MildRacc/MildVR/PCB/Imports/SFH_4556/SFH_4556.step

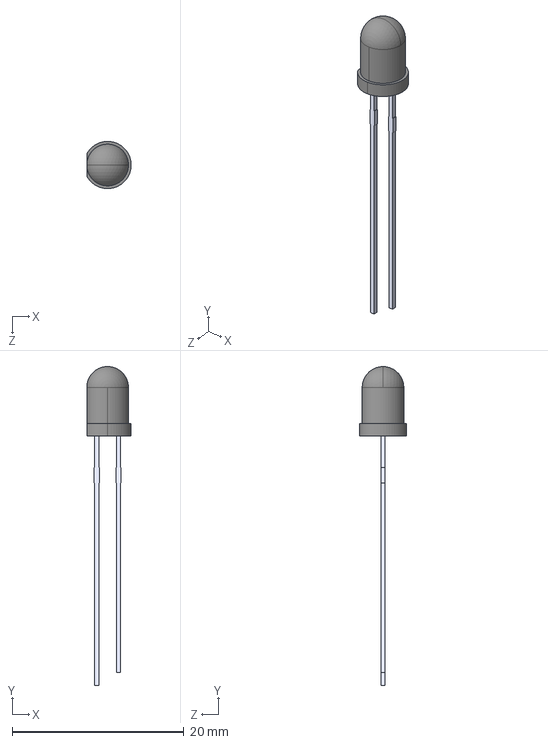
[picture p15: CAD file, 2025-12-30]
PCB/Imports/SFH_4556/SFH_4556.step
5.18 x 37.1 x 5.50 mm
