MildRacc/MildVR/PCB/Imports/(CSI) 20539-050E-01/20539-050E-01.step

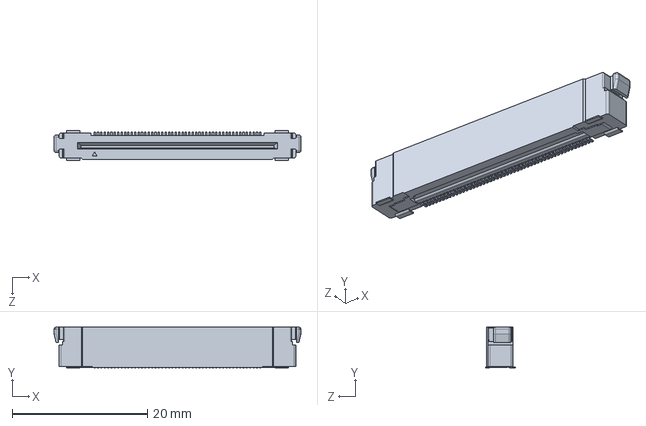
[picture p16: CAD file, 2025-11-03]
PCB/Imports/(CSI) 20539-050E-01/20539-050E-01.step
36.5 x 6.00 x 4.50 mm
