MildRacc/MildVR/PCB/Imports/(Pump)LM27761DSGR/LM27761DSGR.step

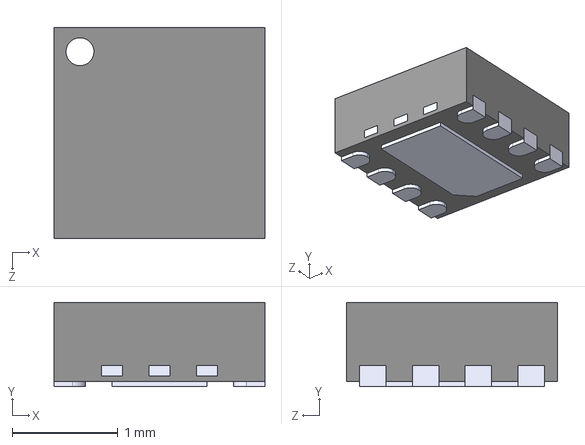
[picture p17: CAD file, 2025-12-31]
PCB/Imports/(Pump)LM27761DSGR/LM27761DSGR.step
2.00 x 0.8 x 2.00 mm
