MildRacc/MildVR/PCB/Imports/CM4IO-KiCAD/CM4_HighSpeed.kicad_sch

## KiCad design PCB/Imports/CM4IO-KiCAD/CM4_HighSpeed.kicad_sch (2025-11-22)

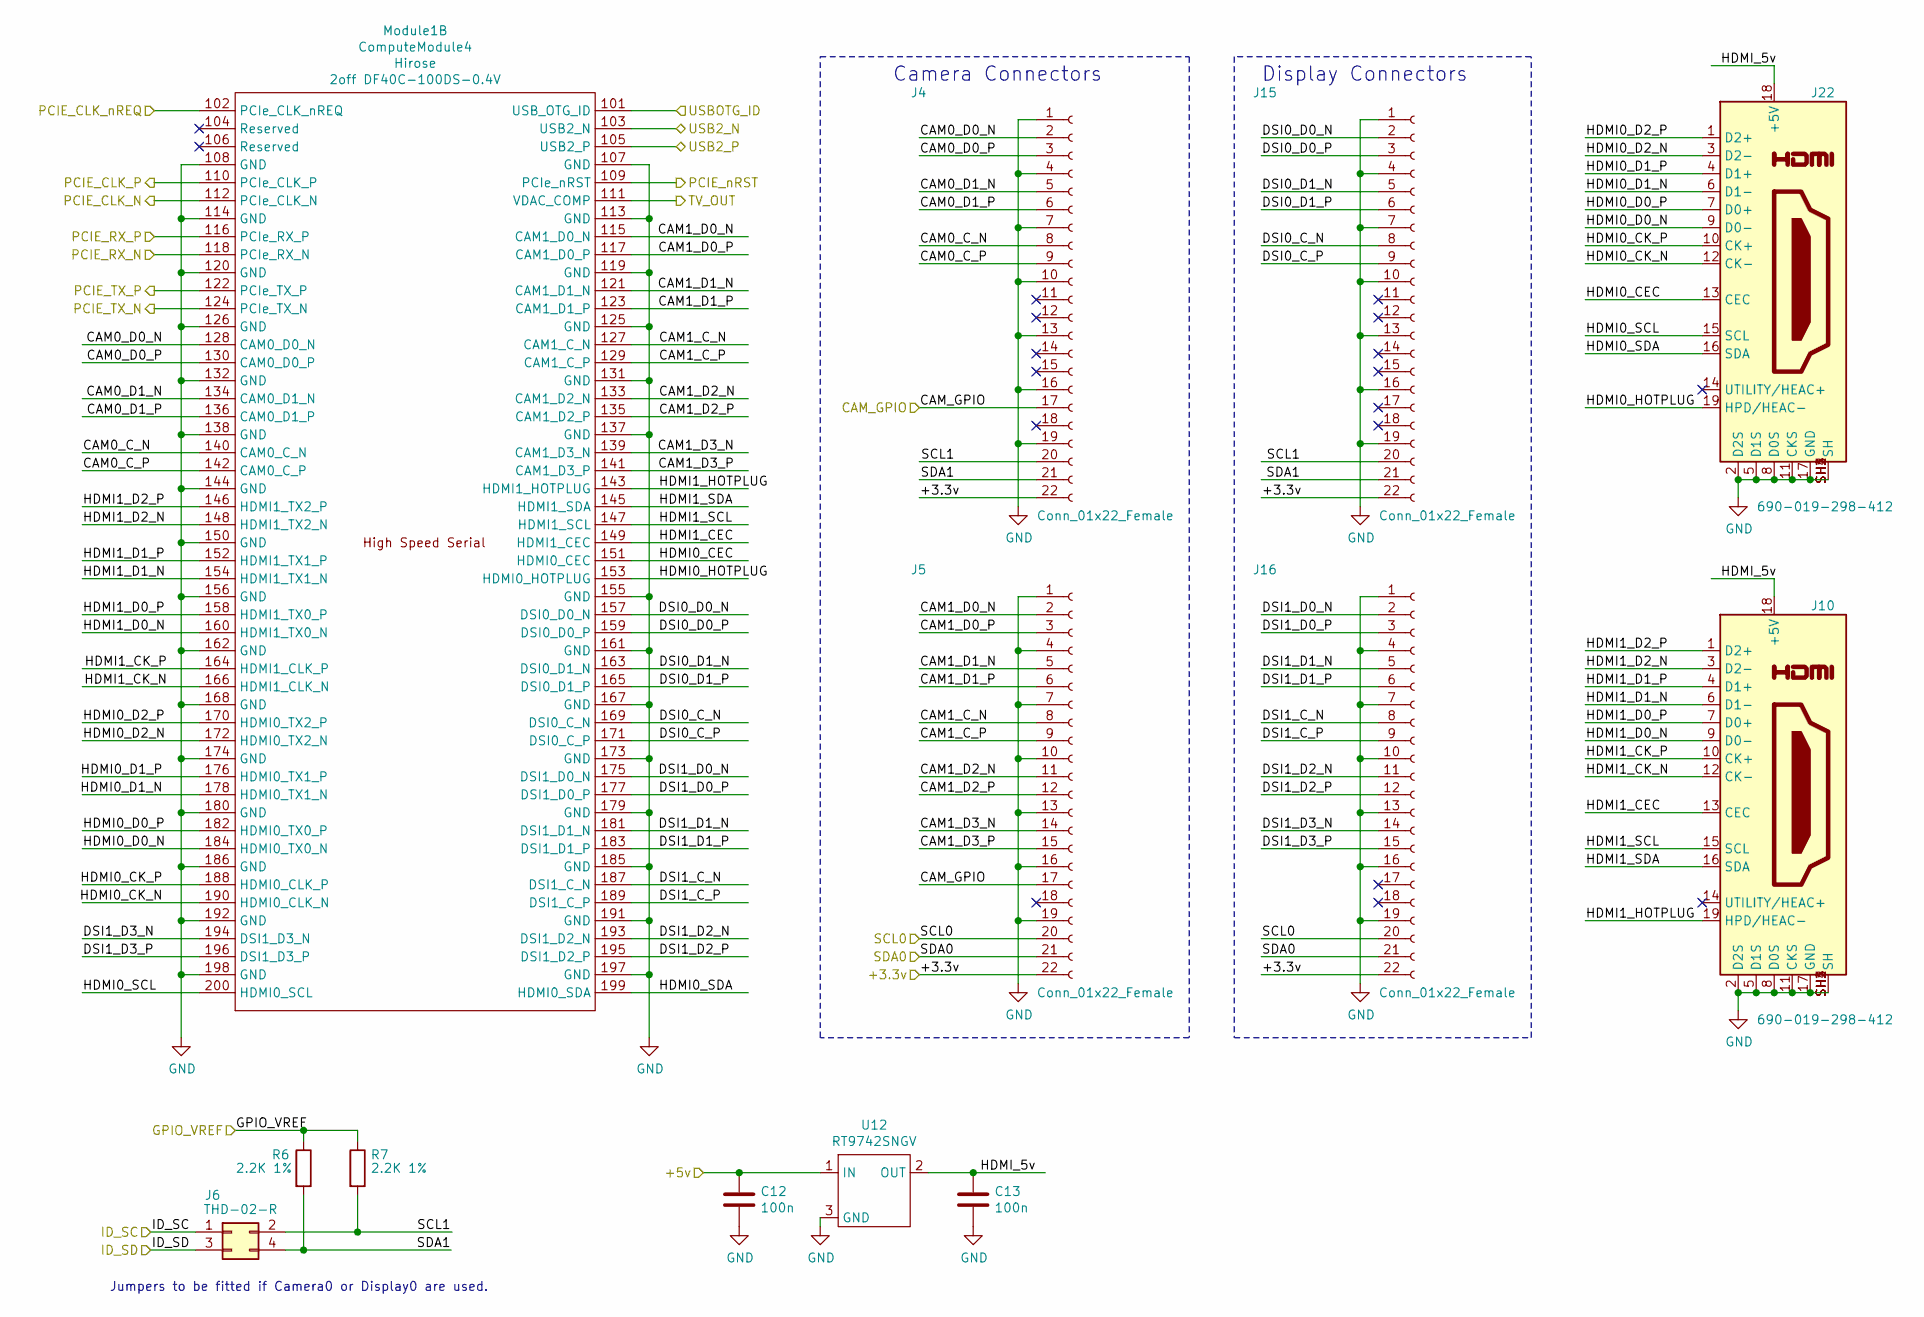
[picture p21: schematic CM4_HighSpeed.kicad_sch]

Parts:
C12, C13: 100n; C_0402_1005Metric; Part Description 0.1uF 10% 16V Ceramic Capacitor X7R 040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
J4, J5, J15, J16: Conn_01x22_Female; Hirose_FH12-22S-0.5SH_1x22-1MP_P0.50mm_Horizontal; Part Description 22 Position FFC, FPC Connector Contacts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
J6: THD-02-R; PinHeader_2x02_P2.54mm_Vertical; Part Description PinHeader_2x02_P2.54mm_Vertical
J10, J22: 690-019-298-412; EDAC 690-019-298-412; Part Description HDMI Connector, Right Angle, 19 Contact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
Module1: ComputeModule4; Raspberry-Pi-4-Compute-Module; Part Description 100 Position Connector Receptacle, Cent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
R6, R7: 2.2K 1%; R_0402_1005Metric; Part Description Resistor 2.2K M1005 1% 63mW
U12: RT9742SNGV; SOT-23; Part Description Power Switch/Driver 1:1 N-Channel 500mA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

Connections:
+3.3v: J4.22, J5.22, J15.22, J16.22
+5v: C12.1, U12.1 (IN)
CAM0_C_N: J4.8, Module1.140 (CAM0_C_N)
CAM0_C_P: J4.9, Module1.142 (CAM0_C_P)
CAM0_D0_N: J4.2, Module1.128 (CAM0_D0_N)
CAM0_D0_P: J4.3, Module1.130 (CAM0_D0_P)
CAM0_D1_N: J4.5, Module1.134 (CAM0_D1_N)
CAM0_D1_P: J4.6, Module1.136 (CAM0_D1_P)
CAM1_C_N: J5.8, Module1.127 (CAM1_C_N)
CAM1_C_P: J5.9, Module1.129 (CAM1_C_P)
CAM1_D0_N: J5.2, Module1.115 (CAM1_D0_N)
CAM1_D0_P: J5.3, Module1.117 (CAM1_D0_P)
CAM1_D1_N: J5.5, Module1.121 (CAM1_D1_N)
CAM1_D1_P: J5.6, Module1.123 (CAM1_D1_P)
CAM1_D2_N: J5.11, Module1.133 (CAM1_D2_N)
CAM1_D2_P: J5.12, Module1.135 (CAM1_D2_P)
CAM1_D3_N: J5.14, Module1.139 (CAM1_D3_N)
CAM1_D3_P: J5.15, Module1.141 (CAM1_D3_P)
CAM_GPIO: J4.17, J5.17
DSI0_C_N: J15.8, Module1.169 (DSI0_C_N)
DSI0_C_P: J15.9, Module1.171 (DSI0_C_P)
DSI0_D0_N: J15.2, Module1.157 (DSI0_D0_N)
DSI0_D0_P: J15.3, Module1.159 (DSI0_D0_P)
DSI0_D1_N: J15.5, Module1.163 (DSI0_D1_N)
DSI0_D1_P: J15.6, Module1.165 (DSI0_D1_P)
DSI1_C_N: J16.8, Module1.187 (DSI1_C_N)
DSI1_C_P: J16.9, Module1.189 (DSI1_C_P)
DSI1_D0_N: J16.2, Module1.175 (DSI1_D0_N)
DSI1_D0_P: J16.3, Module1.177 (DSI1_D0_P)
DSI1_D1_N: J16.5, Module1.181 (DSI1_D1_N)
DSI1_D1_P: J16.6, Module1.183 (DSI1_D1_P)
DSI1_D2_N: J16.11, Module1.193 (DSI1_D2_N)
DSI1_D2_P: J16.12, Module1.195 (DSI1_D2_P)
DSI1_D3_N: J16.14, Module1.194 (DSI1_D3_N)
DSI1_D3_P: J16.15, Module1.196 (DSI1_D3_P)
GND: C12.2, C13.2, J4.1, J4.4, J4.7, J4.10, J4.13, J4.16, J4.19, J5.1, J5.4, J5.7, J5.10, J5.13, J5.16, J5.19, J10.2 (D2S), J10.5 (D1S), J10.8 (D0S), J10.11 (CKS), J10.17 (GND), J10.SH1 (SH), J10.SH2 (SH), J10.SH3 (SH), J10.SH4 (SH), J15.1, J15.4, J15.7, J15.10, J15.13, J15.16, J15.19, J16.1, J16.4, J16.7, J16.10, J16.13, J16.16, J16.19, J22.2 (D2S), J22.5 (D1S), J22.8 (D0S), J22.11 (CKS), J22.17 (GND), J22.SH1 (SH), J22.SH2 (SH), J22.SH3 (SH), J22.SH4 (SH), Module1.107 (GND), Module1.108 (GND), Module1.113 (GND), Module1.114 (GND), Module1.119 (GND), Module1.120 (GND), Module1.125 (GND), Module1.126 (GND), Module1.131 (GND), Module1.132 (GND), Module1.137 (GND), Module1.138 (GND), Module1.144 (GND), Module1.150 (GND), Module1.155 (GND), Module1.156 (GND), Module1.161 (GND), Module1.162 (GND), Module1.167 (GND), Module1.168 (GND), Module1.173 (GND), Module1.174 (GND), Module1.179 (GND), Module1.180 (GND), Module1.185 (GND), Module1.186 (GND), Module1.191 (GND), Module1.192 (GND), Module1.197 (GND), Module1.198 (GND), U12.3 (GND)
GPIO_VREF: R6.1, R7.1
HDMI0_CEC: J22.13 (CEC), Module1.151 (HDMI0_CEC)
HDMI0_CK_N: J22.12 (CK-), Module1.190 (HDMI0_CLK_N)
HDMI0_CK_P: J22.10 (CK+), Module1.188 (HDMI0_CLK_P)
HDMI0_D0_N: J22.9 (D0-), Module1.184 (HDMI0_TX0_N)
HDMI0_D0_P: J22.7 (D0+), Module1.182 (HDMI0_TX0_P)
HDMI0_D1_N: J22.6 (D1-), Module1.178 (HDMI0_TX1_N)
HDMI0_D1_P: J22.4 (D1+), Module1.176 (HDMI0_TX1_P)
HDMI0_D2_N: J22.3 (D2-), Module1.172 (HDMI0_TX2_N)
HDMI0_D2_P: J22.1 (D2+), Module1.170 (HDMI0_TX2_P)
HDMI0_HOTPLUG: J22.19 (HPD/HEAC-), Module1.153 (HDMI0_HOTPLUG)
HDMI0_SCL: J22.15 (SCL), Module1.200 (HDMI0_SCL)
HDMI0_SDA: J22.16 (SDA), Module1.199 (HDMI0_SDA)
HDMI1_CEC: J10.13 (CEC), Module1.149 (HDMI1_CEC)
HDMI1_CK_N: J10.12 (CK-), Module1.166 (HDMI1_CLK_N)
HDMI1_CK_P: J10.10 (CK+), Module1.164 (HDMI1_CLK_P)
HDMI1_D0_N: J10.9 (D0-), Module1.160 (HDMI1_TX0_N)
HDMI1_D0_P: J10.7 (D0+), Module1.158 (HDMI1_TX0_P)
HDMI1_D1_N: J10.6 (D1-), Module1.154 (HDMI1_TX1_N)
HDMI1_D1_P: J10.4 (D1+), Module1.152 (HDMI1_TX1_P)
HDMI1_D2_N: J10.3 (D2-), Module1.148 (HDMI1_TX2_N)
HDMI1_D2_P: J10.1 (D2+), Module1.146 (HDMI1_TX2_P)
HDMI1_HOTPLUG: J10.19 (HPD/HEAC-), Module1.143 (HDMI1_HOTPLUG)
HDMI1_SCL: J10.15 (SCL), Module1.147 (HDMI1_SCL)
HDMI1_SDA: J10.16 (SDA), Module1.145 (HDMI1_SDA)
HDMI_5v: C13.1, J10.18 (+5V), J22.18 (+5V), U12.2 (OUT)
ID_SC: J6.1
ID_SD: J6.3
PCIE_CLK_N: Module1.112 (PCIe_CLK_N)
PCIE_CLK_P: Module1.110 (PCIe_CLK_P)
PCIE_CLK_nREQ: Module1.102 (PCIe_CLK_nREQ)
PCIE_RX_N: Module1.118 (PCIe_RX_N)
PCIE_RX_P: Module1.116 (PCIe_RX_P)
PCIE_TX_N: Module1.124 (PCIe_TX_N)
PCIE_TX_P: Module1.122 (PCIe_TX_P)
PCIE_nRST: Module1.109 (PCIe_nRST)
SCL0: J5.20, J16.20
SCL1: J4.20, J6.2, J15.20, R7.2
SDA0: J5.21, J16.21
SDA1: J4.21, J6.4, J15.21, R6.2
TV_OUT: Module1.111 (VDAC_COMP)
USB2_N: Module1.103 (USB2_N)
USB2_P: Module1.105 (USB2_P)
USBOTG_ID: Module1.101 (USB_OTG_ID)

Notes on the sheet:
Jumpers to be fitted if Camera0 or Display0 are used.
Camera Connectors
Display Connectors
