MildRacc/MildVR/PCB/Imports/CM4IO-KiCAD/PSUs.kicad_sch

## KiCad design PCB/Imports/CM4IO-KiCAD/PSUs.kicad_sch (2025-11-22)

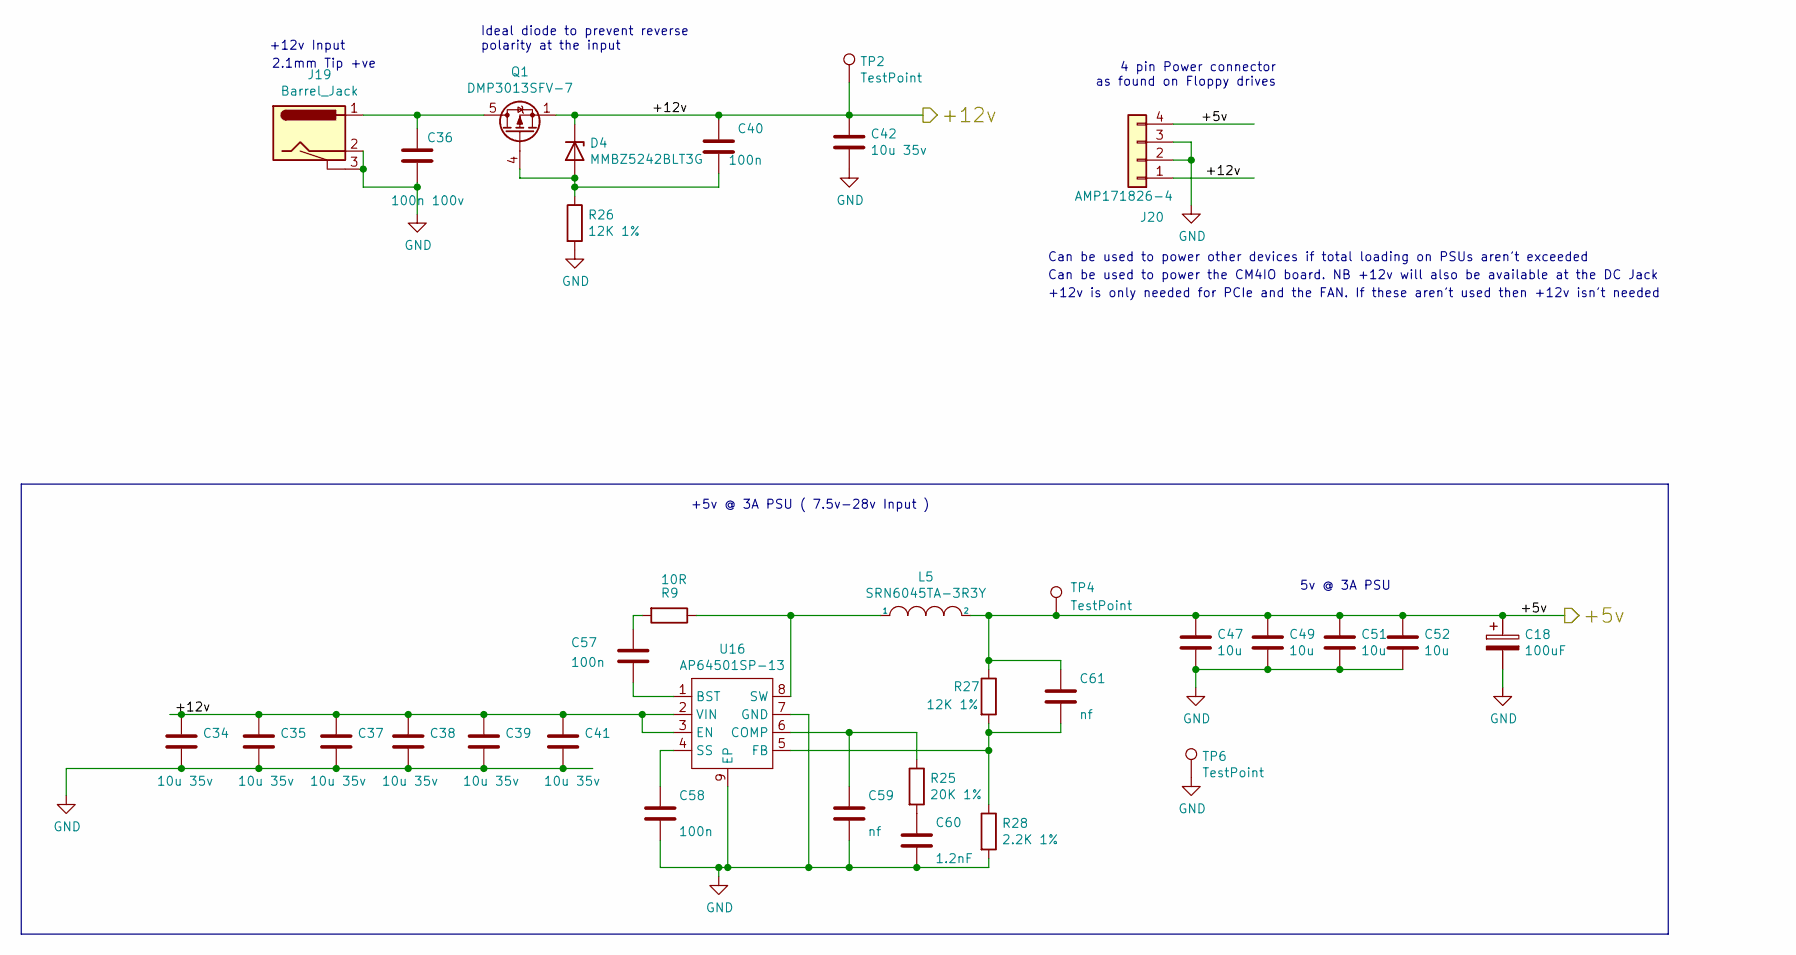
[picture p23: schematic PSUs.kicad_sch]

Parts:
C18: 100uF; CP_EIA-7343-31_Kemet-D; Part Description Capacitor, SP-Cap, 100u, 6.3V, 15mR ESR
C34, C35, C37, C38, C39, C41, C42: 10u 35v; C_0805_2012Metric; Part Description 10uF 10% or 20% 35V Ceramic Capacitor X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
C36: 100n 100v; C_0402_1005Metric; Part Description 0.1uF 10% 100V Ceramic Capacitor X5R 04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
C40, C57, C58: 100n; C_0402_1005Metric; Part Description 0.1uF 10% 16V Ceramic Capacitor X7R 040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
C47, C49, C51, C52: 10u; C_0805_2012Metric; Part Description 10uF 10% 10V Ceramic Capacitor X7R 0805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
C59: nf; C_0402_1005Metric
C60: 1.2nF; C_0402_1005Metric; Part Description 1200pF 10% 10V Ceramic Capacitor X5R 04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
C61: nf; C_0402_1005Metric; Part Description 220 pF, 50 V, 0402 [1005 Metric], ± 5%,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
D4: MMBZ5242BLT3G; D_SOT-23_ANK; Part Description Zener Diode 12V 225mW 5% Surface Mount 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
J19: Barrel_Jack; BarrelJack_Horizontal; Part Description DC Power Connectors PCB 2.1MM
J20: AMP171826-4; TE_171826-4; Part Description Wire-To-Board Connector, Right Angle, 2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
L5: SRN6045TA-3R3Y; L_Bourns_SRN6045TA; Part Description 3.3µH Semi-Shielded Wirewound Inductor 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
Q1: DMP3013SFV-7; Diodes_PowerDI3333-8; Part Description DMP3013SFV-7 - Power MOSFET, P Channel,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
R9: 10R; R_0402_1005Metric; Part Description Resistor 10R M1005 1% 63mW
R25: 20K 1%; R_0402_1005Metric; Part Description Resistor 20K M1005 1% 63mW
R26, R27: 12K 1%; R_0402_1005Metric; Part Description Resistor 12K M1005 1% 63mW
R28: 2.2K 1%; R_0402_1005Metric; Part Description Resistor 2.2K M1005 1% 63mW
TP2, TP4, TP6: TestPoint; TestPoint_Pad_2.0x2.0mm
U16: AP64501SP-13; SOIC-8-1EP_3.9x4.9mm_P1.27mm_EP2.95x4.9mm_Mask2.71x3.4mm_Th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; Part Description Buck Switching Regulator IC Positive Ad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

Connections:
+5v: C18.1, C47.1, C49.1, C51.1, C52.1, C61.1, J20.4, L5.2, R27.1, TP4.1
+12v: C34.1, C35.1, C37.1, C38.1, C39.1, C40.1, C41.1, C42.1, D4.1 (K), J20.1, Q1.1 (S), Q1.2 (S), Q1.3 (S), TP2.1, U16.2 (VIN), U16.3 (EN)
GND: C18.2, C34.2, C35.2, C36.2, C37.2, C38.2, C39.2, C41.2, C42.2, C47.2, C49.2, C51.2, C52.2, C58.2, C59.2, C60.2, J19.2, J19.3, J20.2, J20.3, R26.2, R28.2, TP6.1, U16.7 (GND), U16.9 (EP)
unnamed: C36.1, J19.1, Q1.5 (D)
unnamed: C40.2, D4.2 (A), Q1.4 (G), R26.1
unnamed: C57.1, R9.2
unnamed: C57.2, U16.1 (BST)
unnamed: C58.1, U16.4 (SS)
unnamed: C59.1, R25.1, U16.6 (COMP)
unnamed: C60.1, R25.2
unnamed: C61.2, R27.2, R28.1, U16.5 (FB)
unnamed: L5.1, R9.1, U16.8 (SW)

Notes on the sheet:
+12v Input
Can be used to power other devices if total loading on PSUs aren't exceeded
5v @ 3A PSU
+12v is only needed for PCIe and the FAN. If these aren't used then +12v isn't needed
Can be used to power the CM4IO board. NB +12v will also be available at the DC Jack
2.1mm Tip +ve
Ideal diode to prevent reverse polarity at the input
4 pin Power connector as found on Floppy drives
+5v @ 3A PSU ( 7.5v-28v Input )
